Aurekana/SwBus/3D-STL/ChargeNub.dxf

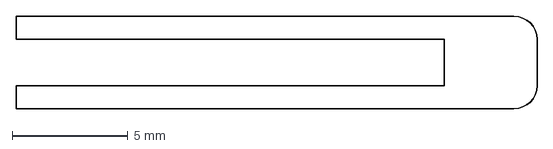
[picture p17: CAD file, 2020-02-20]
3D-STL/ChargeNub.dxf
22.5 x 4.00 mm
