Aurekana/SwBus/3D-STL/23-Cylinder.stl

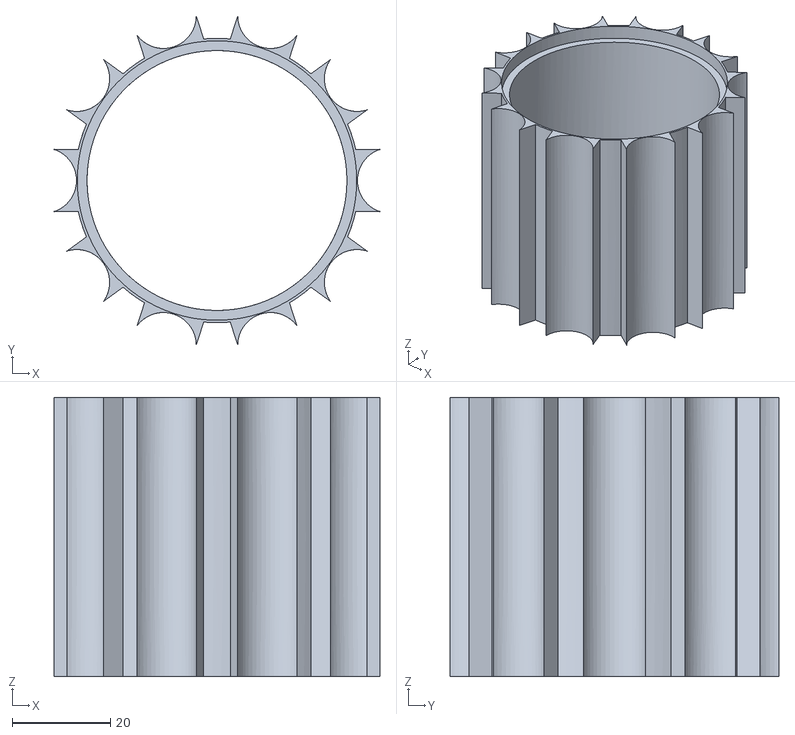
[picture p18: CAD file, 2020-02-20]
3D-STL/23-Cylinder.stl
66.4 x 67.1 x 57.0
