Aurekana/SwBus/3D-STL/19a-StockBack.stl

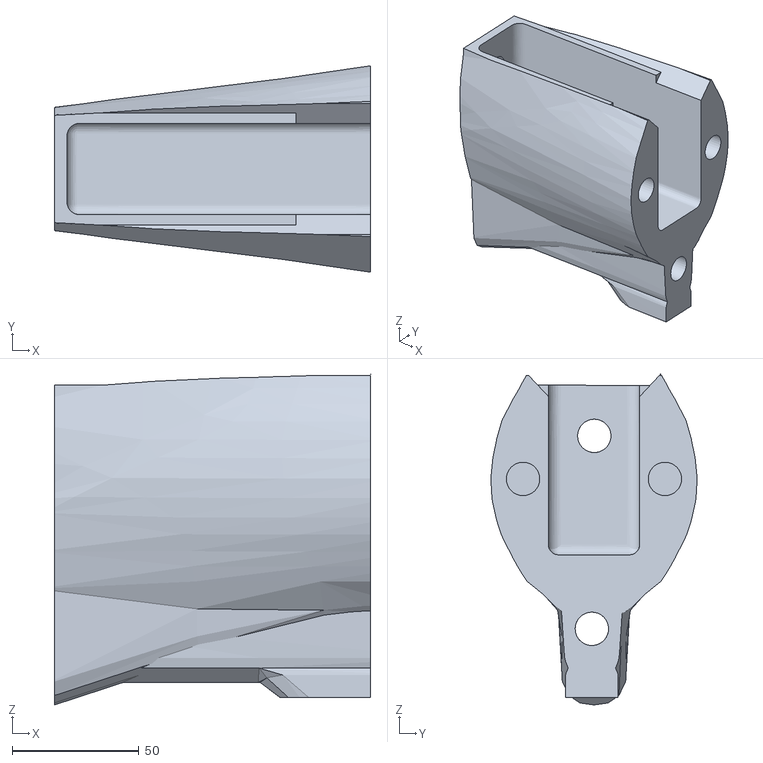
[picture p19: CAD file, 2020-02-20]
3D-STL/19a-StockBack.stl
125.0 x 81.6 x 130.8
