Aurekana/SwBus/3D-STL/33-hud.stl

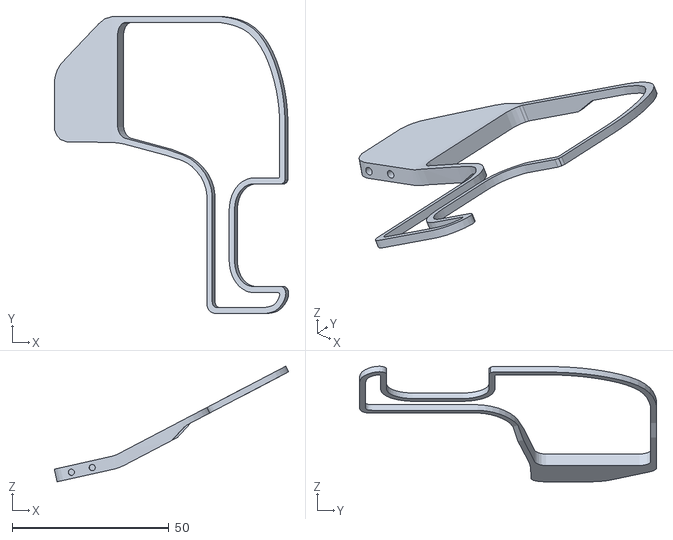
[picture p20: CAD file, 2020-02-20]
3D-STL/33-hud.stl
74.7 x 94.7 x 36.9
