Aurekana/SwBus/3D-STL/19-StockBack.stl

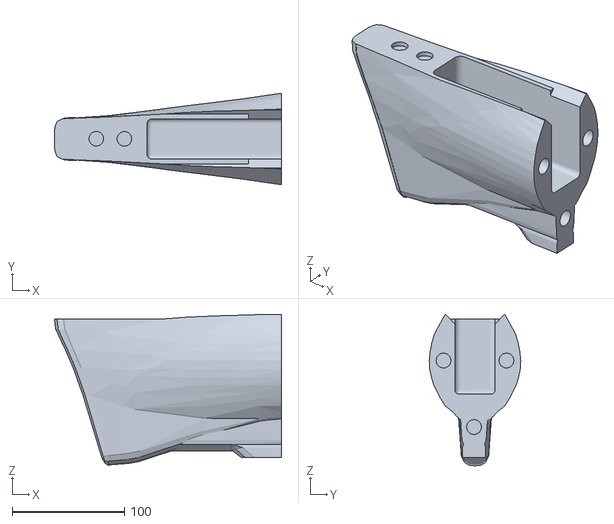
[picture p21: CAD file, 2020-02-20]
3D-STL/19-StockBack.stl
202.3 x 81.6 x 135.4
