Aurekana/SwBus/3D-STL/31-BatCover.stl

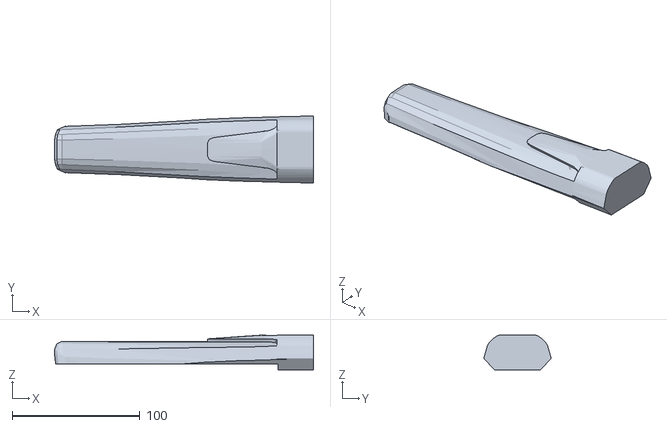
[picture p22: CAD file, 2020-02-20]
3D-STL/31-BatCover.stl
203.1 x 52.7 x 27.3
