Aurekana/SwBus/3D-STL/27b-MagCover.stl

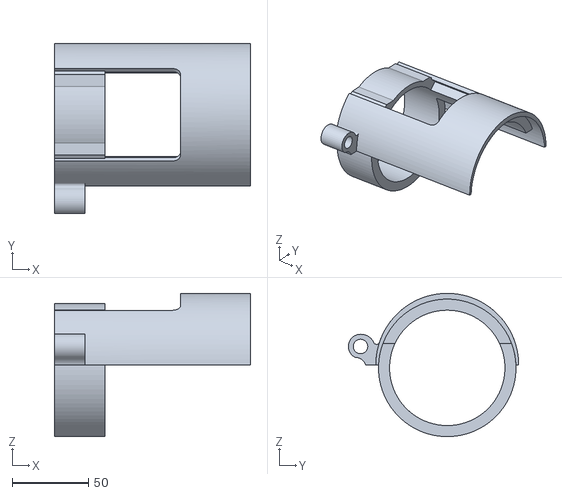
[picture p23: CAD file, 2020-02-20]
3D-STL/27b-MagCover.stl
128.2 x 111.5 x 93.8
