Aurekana/SwBus/3D-STL/30ORCUT-ChargePlate.stl

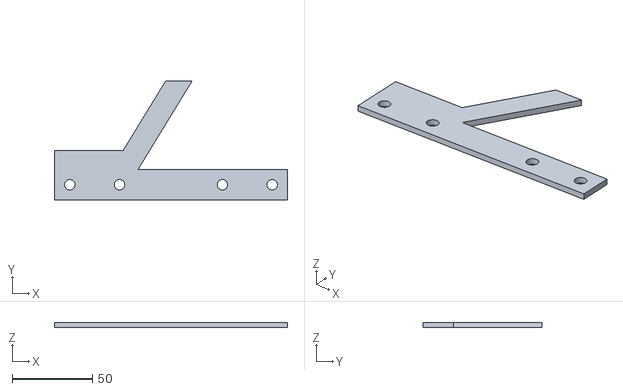
[picture p24: CAD file, 2020-02-20]
3D-STL/30ORCUT-ChargePlate.stl
145.0 x 74.1 x 3.17
