Aurekana/SwBus/3D-STL/28-C-Mag_Cap_60.stl

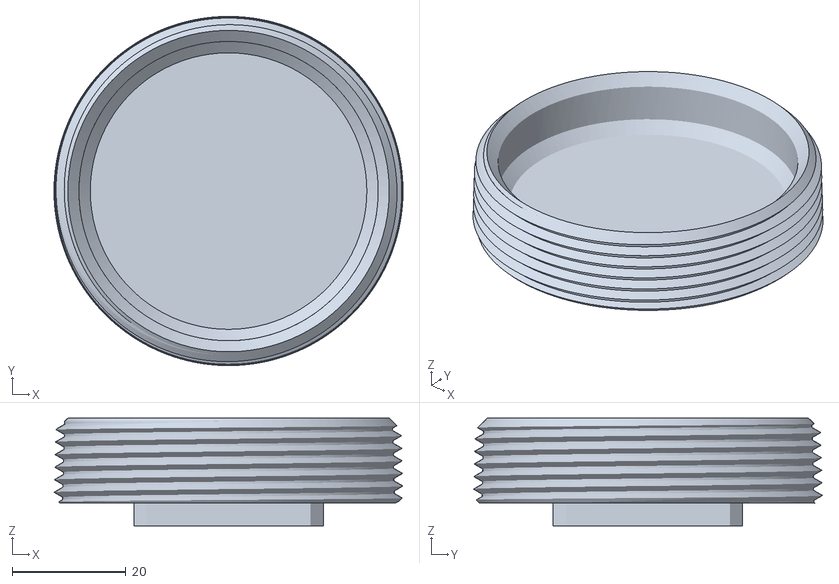
[picture p25: CAD file, 2020-02-20]
3D-STL/28-C-Mag_Cap_60.stl
61.3 x 61.4 x 18.9
