Aurekana/SwBus/3D-STL/hud.dxf

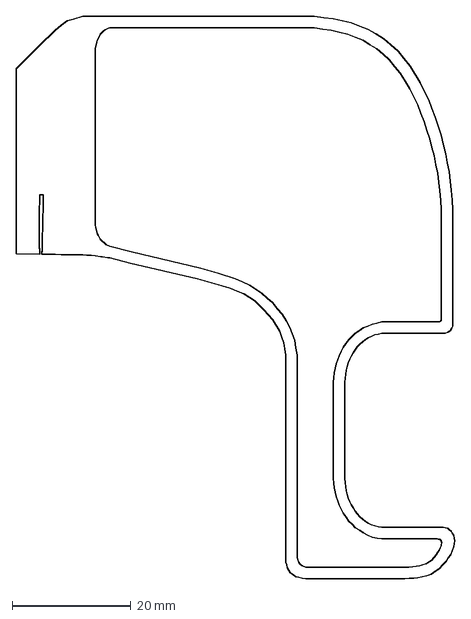
[picture p26: CAD file, 2020-02-20]
3D-STL/hud.dxf
73.8 x 94.7 mm
