Aurekana/SwBus/3D-STL/19b-BackStock.stl

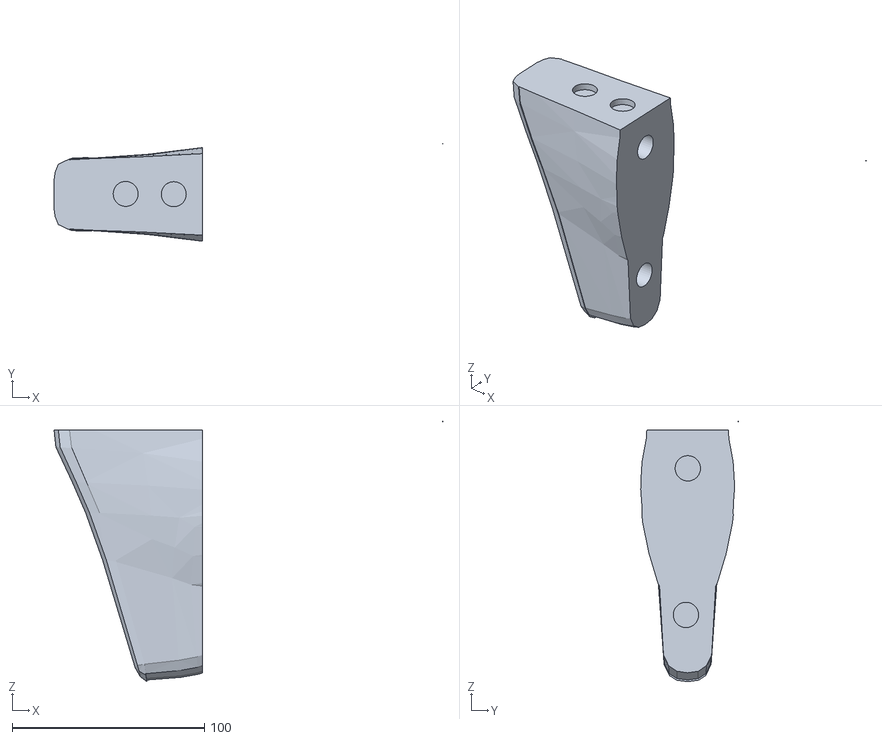
[picture p27: CAD file, 2020-02-20]
3D-STL/19b-BackStock.stl
202.3 x 50.7 x 135.4
