Aurekana/SwBus/3D-STL/Handle_cut.dxf

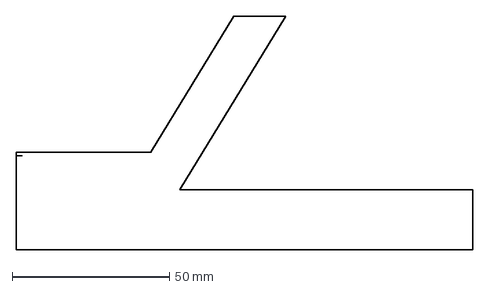
[picture p28: CAD file, 2020-02-20]
3D-STL/Handle_cut.dxf
145.0 x 74.1 mm
