Aurekana/SwBus/3D-STL/28z-Magazine_Beer.stl

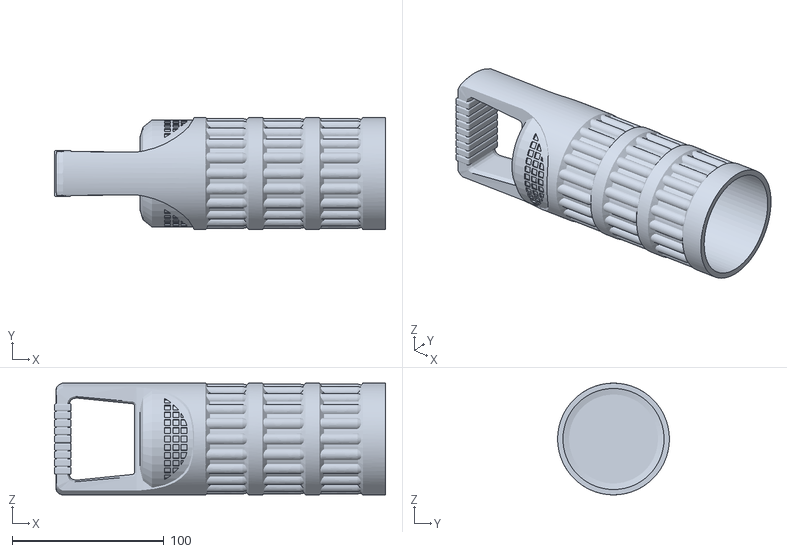
[picture p29: CAD file, 2020-02-20]
3D-STL/28z-Magazine_Beer.stl
217.8 x 73.5 x 73.5
