Aurekana/SwBus/3D-STL/17-MagBack.stl

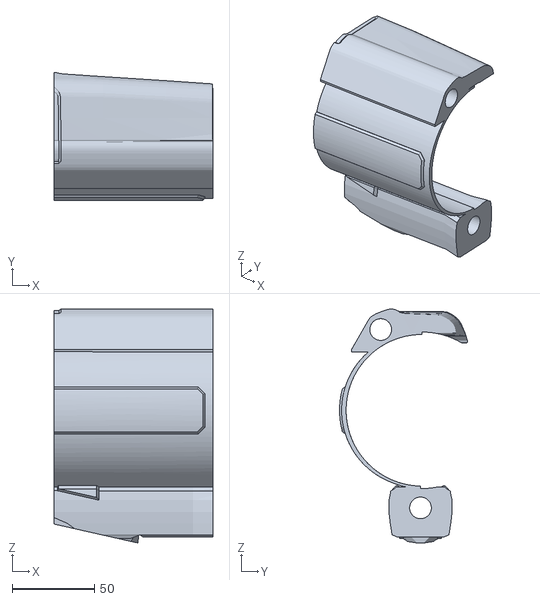
[picture p30: CAD file, 2020-02-20]
3D-STL/17-MagBack.stl
96.4 x 77.6 x 142.0
