Aurekana/SwBus/3D-STL/28zz-Mag-Cont.stl

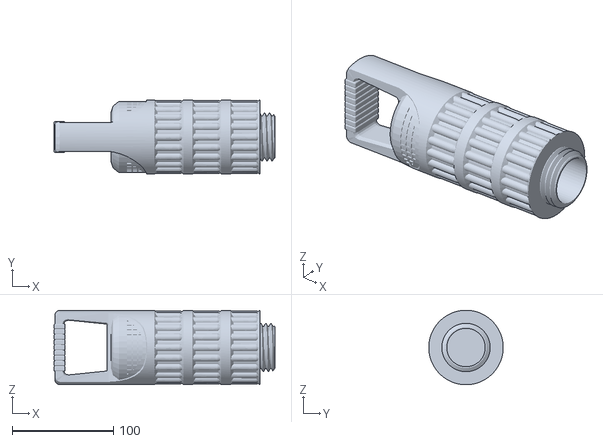
[picture p31: CAD file, 2020-02-20]
3D-STL/28zz-Mag-Cont.stl
218.3 x 73.5 x 73.5
