Aurekana/SwBus/3D-STL/25-Grip.stl

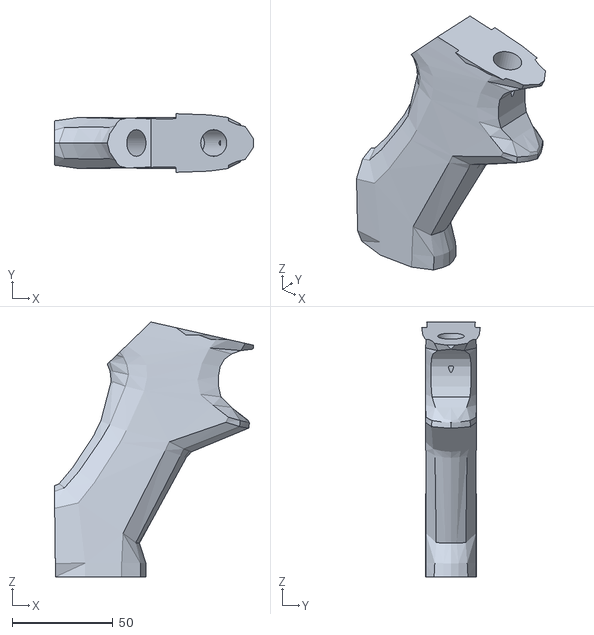
[picture p32: CAD file, 2020-02-20]
3D-STL/25-Grip.stl
98.8 x 29.1 x 126.4
