Aurekana/SwBus/3D-STL/28-Magazine_150.stl

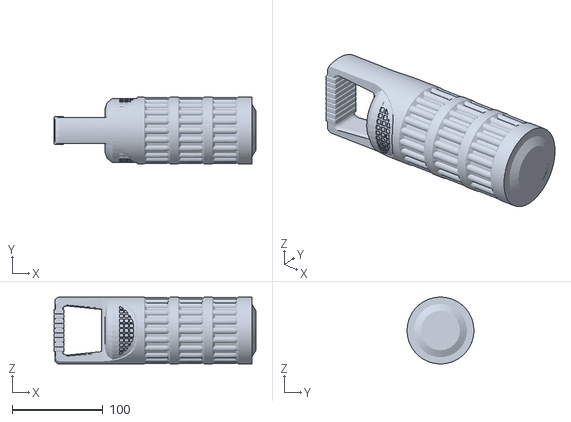
[picture p33: CAD file, 2020-02-20]
3D-STL/28-Magazine_150.stl
222.3 x 73.5 x 73.5
