Aurekana/SwBus/3D-STL/27-MagCover.stl

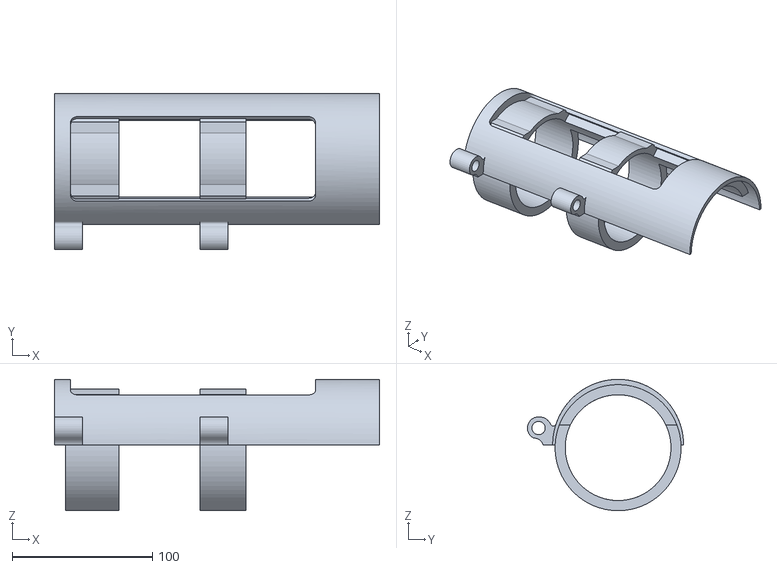
[picture p34: CAD file, 2020-02-20]
3D-STL/27-MagCover.stl
232.0 x 111.5 x 93.7
