Aurekana/SwBus/3D-STL/07-ChargeHandle.stl

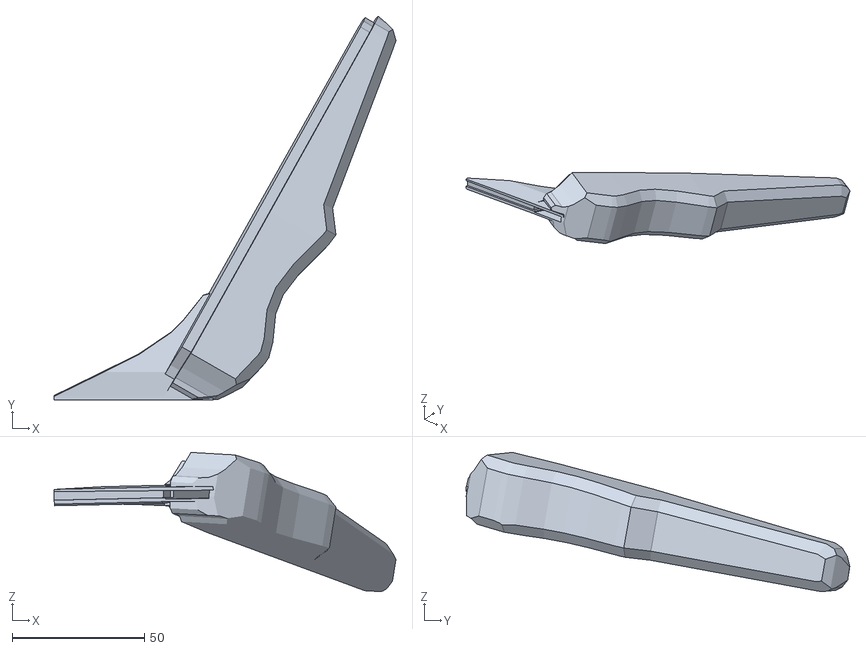
[picture p35: CAD file, 2020-02-20]
3D-STL/07-ChargeHandle.stl
129.2 x 145.0 x 52.6
