Aurekana/SwBus/3D-STL/11-Cylinder.stl

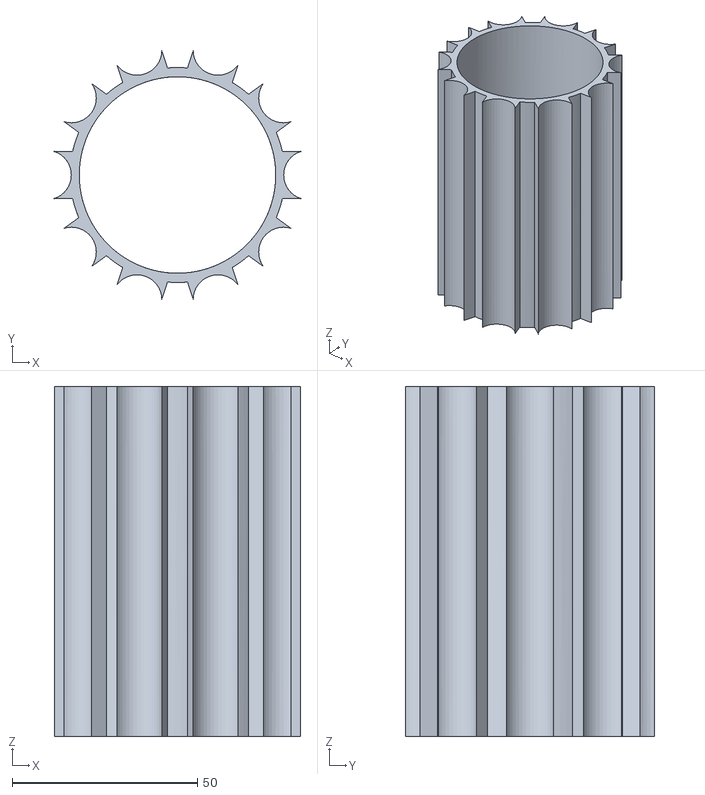
[picture p36: CAD file, 2020-02-20]
3D-STL/11-Cylinder.stl
66.4 x 67.1 x 94.4
