Aurekana/SwBus/3D-STL/15-PotDoor.stl

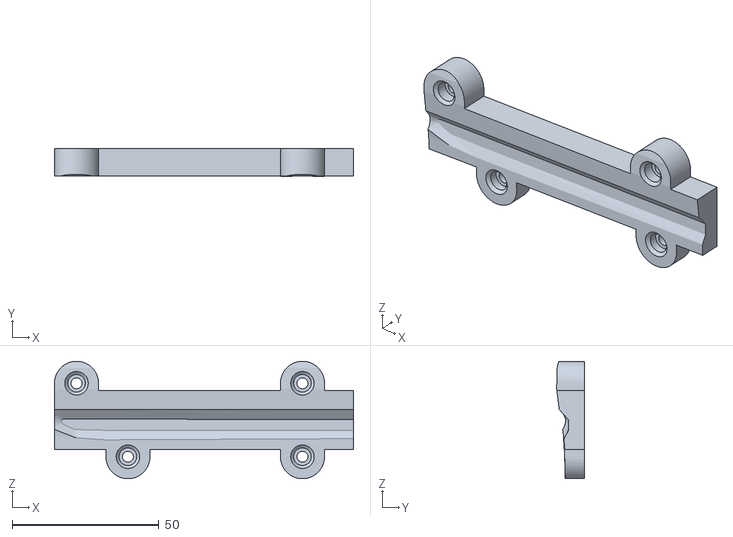
[picture p37: CAD file, 2020-02-20]
3D-STL/15-PotDoor.stl
101.8 x 9.44 x 40.0
