Aurekana/SwBus/3D-STL/09-ChargeUpper.stl

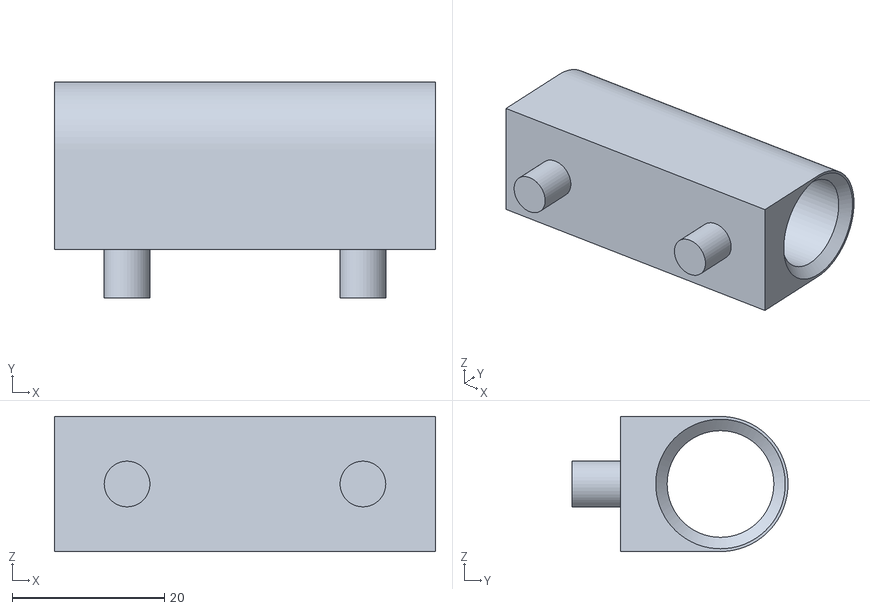
[picture p38: CAD file, 2020-02-20]
3D-STL/09-ChargeUpper.stl
50.0 x 28.4 x 17.7
