Aurekana/SwBus/3D-STL/10-Ring3.stl

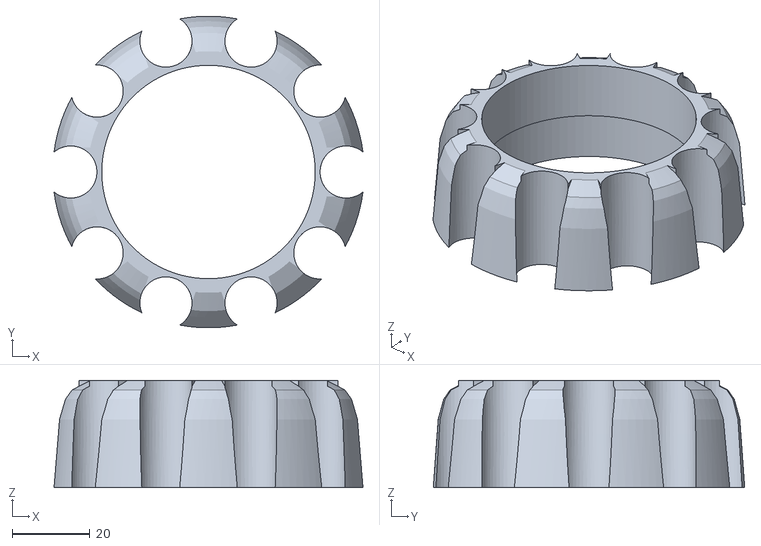
[picture p39: CAD file, 2020-02-20]
3D-STL/10-Ring3.stl
79.3 x 80.0 x 27.5
