Aurekana/SwBus/3D-STL/13-Spacer.stl

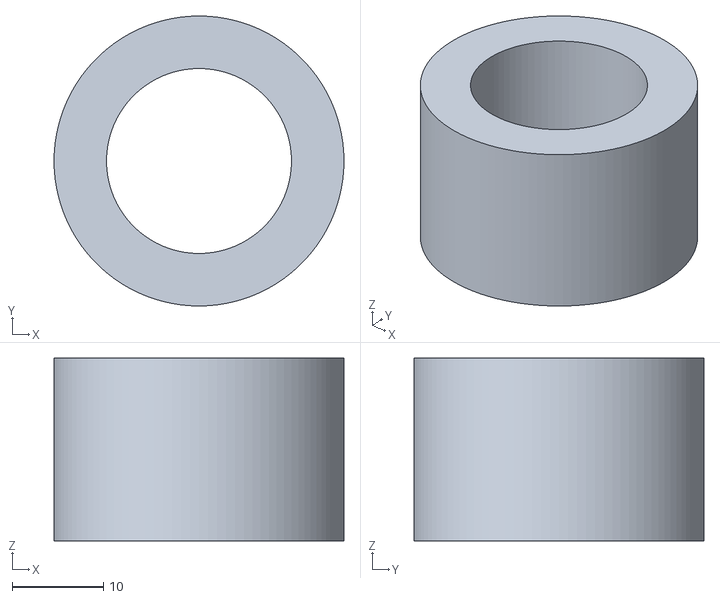
[picture p40: CAD file, 2020-02-20]
3D-STL/13-Spacer.stl
31.8 x 31.8 x 20.0
