Aurekana/SwBus/3D-STL/08-ChargeLower.stl

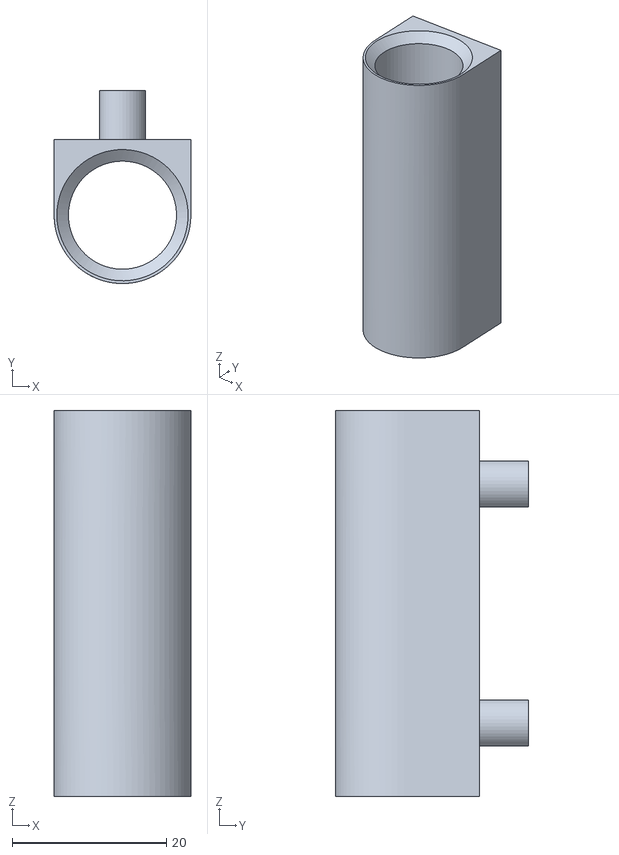
[picture p41: CAD file, 2020-02-20]
3D-STL/08-ChargeLower.stl
17.7 x 25.0 x 50.0
