Aurekana/SwBus/3D-STL/14-Ring2.stl

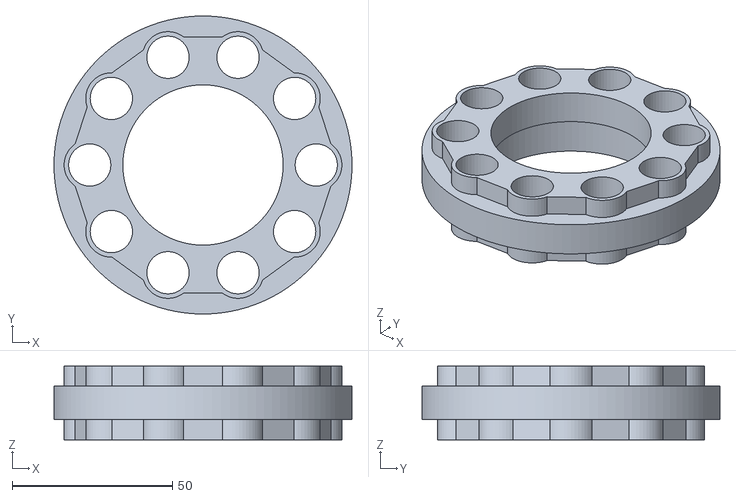
[picture p42: CAD file, 2020-02-20]
3D-STL/14-Ring2.stl
93.0 x 93.0 x 23.0
