Aurekana/SwBus/3D-STL/04-PotDoor.stl

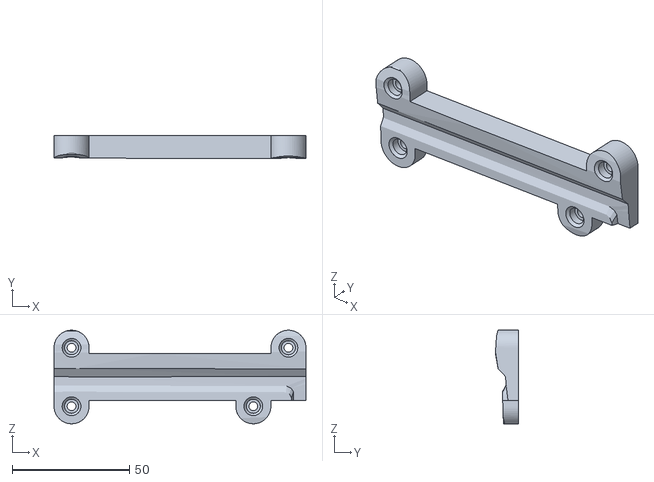
[picture p43: CAD file, 2020-02-20]
3D-STL/04-PotDoor.stl
107.7 x 9.87 x 40.0
