Aurekana/SwBus/3D-STL/01-Front.stl

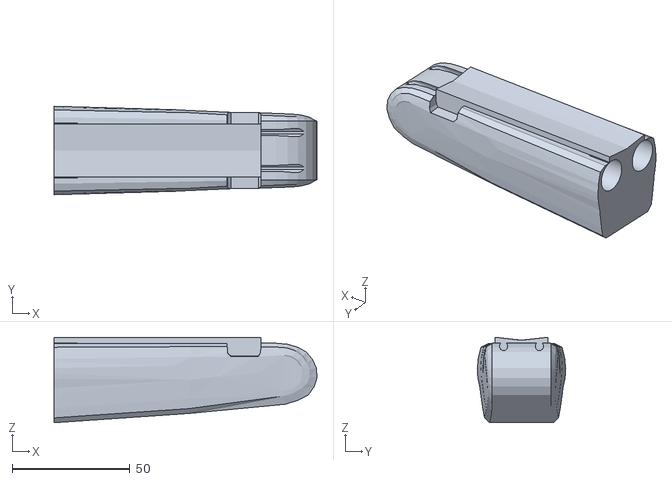
[picture p44: CAD file, 2020-02-20]
3D-STL/01-Front.stl
111.6 x 37.6 x 36.3
