Aurekana/SwBus/3D-STL/05-Front.stl

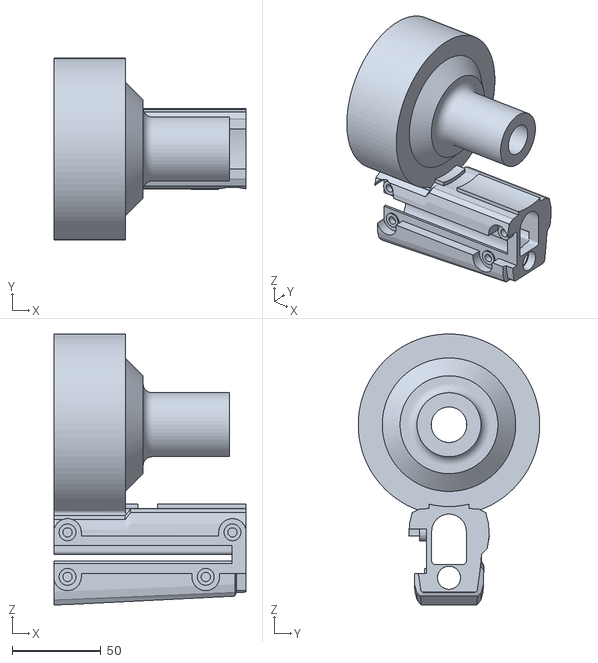
[picture p45: CAD file, 2020-02-20]
3D-STL/05-Front.stl
107.7 x 102.0 x 152.3
