Aurekana/SwBus/3D-STL/02-Front.stl

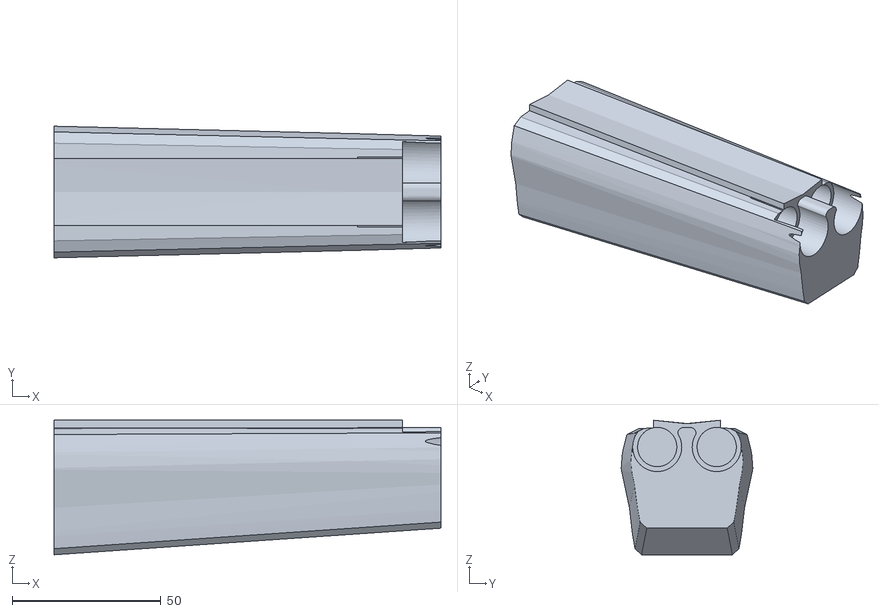
[picture p46: CAD file, 2020-02-20]
3D-STL/02-Front.stl
130.0 x 44.2 x 45.2
