Aurekana/SwBus/3D-STL/03-Front.stl

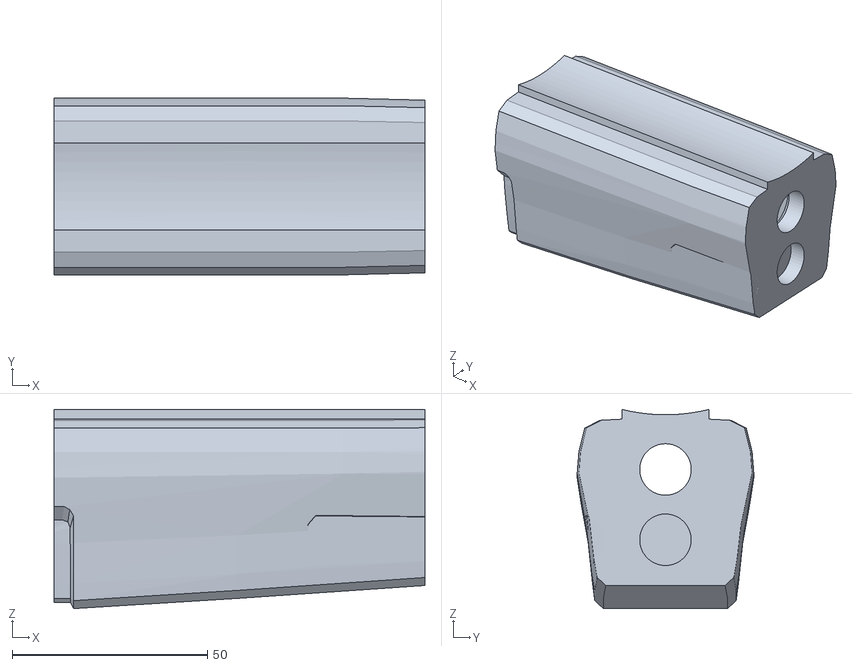
[picture p47: CAD file, 2020-02-20]
3D-STL/03-Front.stl
95.0 x 45.3 x 51.0
