Aurekana/SwBus/3D-STL/06-Ring4.stl

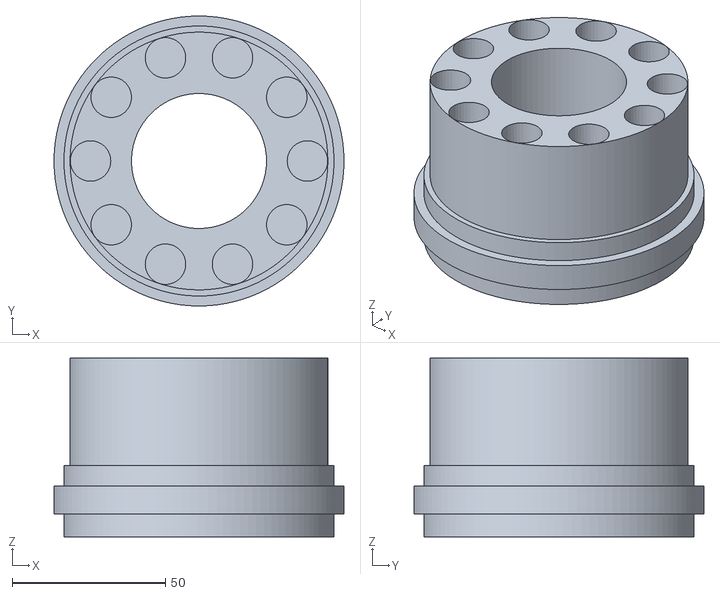
[picture p48: CAD file, 2020-02-20]
3D-STL/06-Ring4.stl
94.5 x 94.5 x 58.2
