Aurekana/SwBus/Assembly/001-Charge_Handle_Assembly.PNG

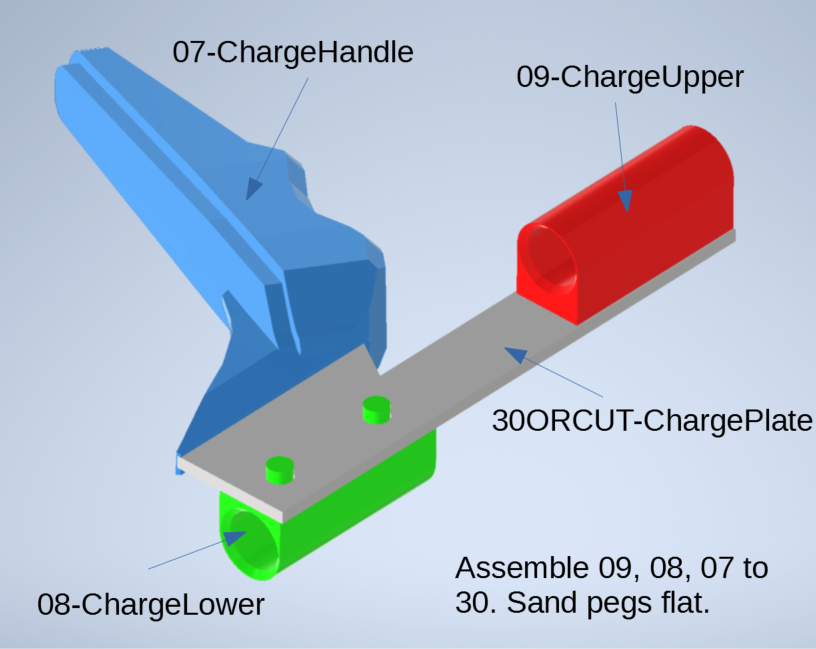
Assembly/001-Charge_Handle_Assembly.PNG
