Aurekana/SwBus/Assembly/002B-Trigger_Wiring_Guide.PNG

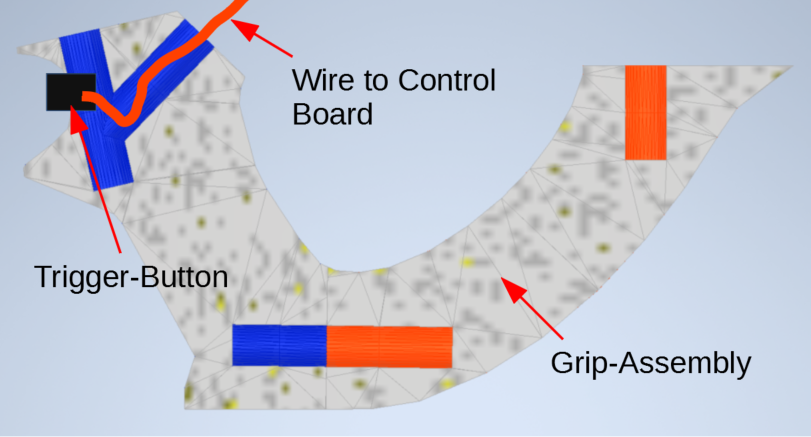
Assembly/002B-Trigger_Wiring_Guide.PNG
