Aurekana/SwBus/Assembly/003-Heat_Set_Insert_Install.PNG

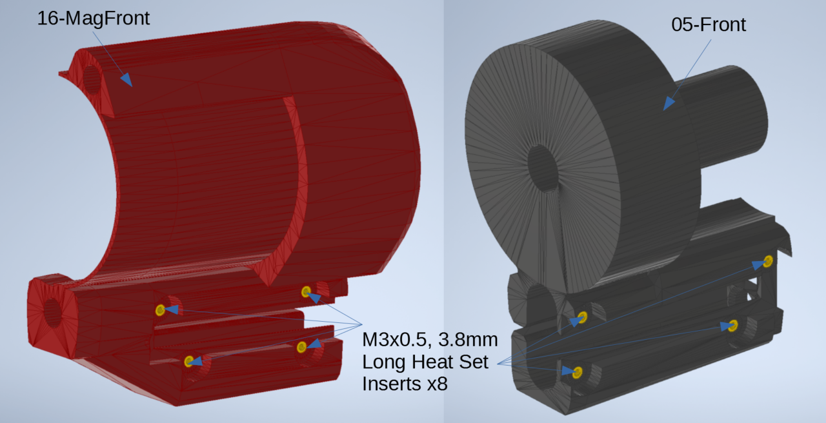
Assembly/003-Heat_Set_Insert_Install.PNG
