Aurekana/SwBus/Assembly/004-Charge_Handle_to_Body_Assembly.PNG

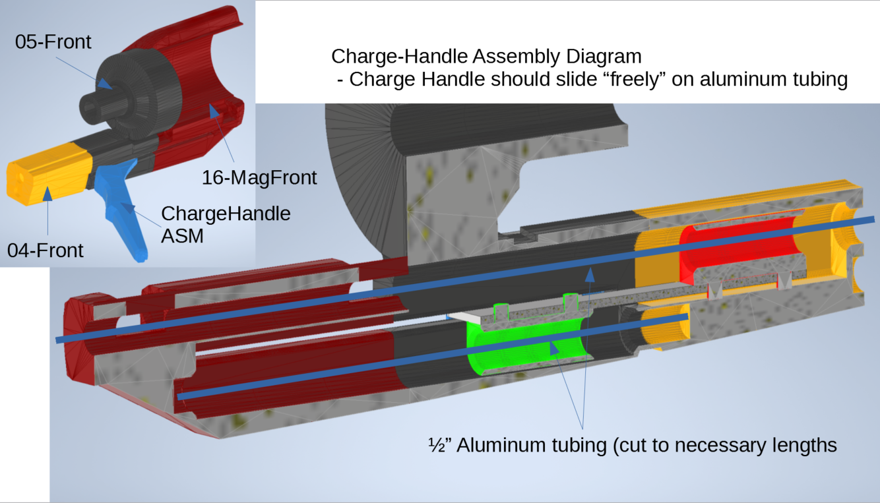
Assembly/004-Charge_Handle_to_Body_Assembly.PNG
