Aurekana/SwBus/Assembly/005A-Mag_Cover_Assembly.PNG

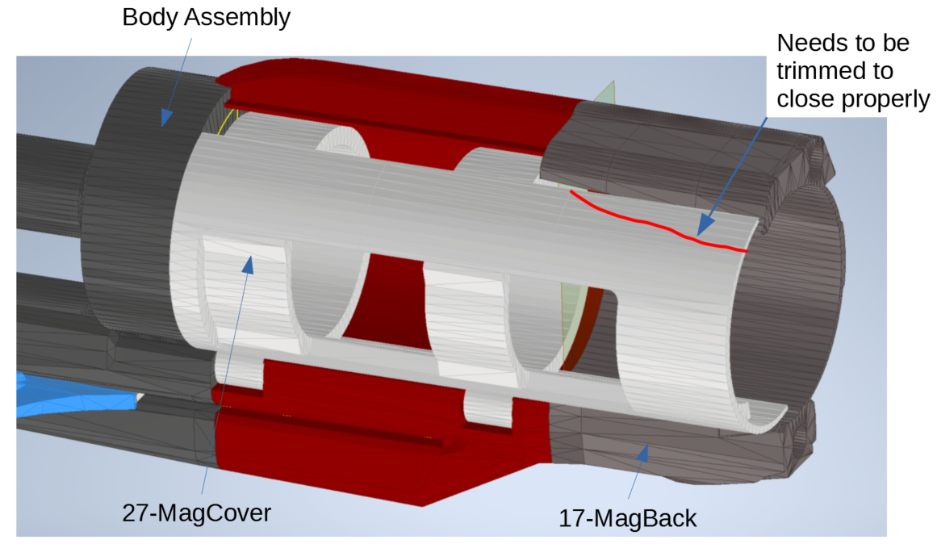
Assembly/005A-Mag_Cover_Assembly.PNG
