Aurekana/SwBus/Assembly/005B-Mag_Cover_Rod_Install.PNG

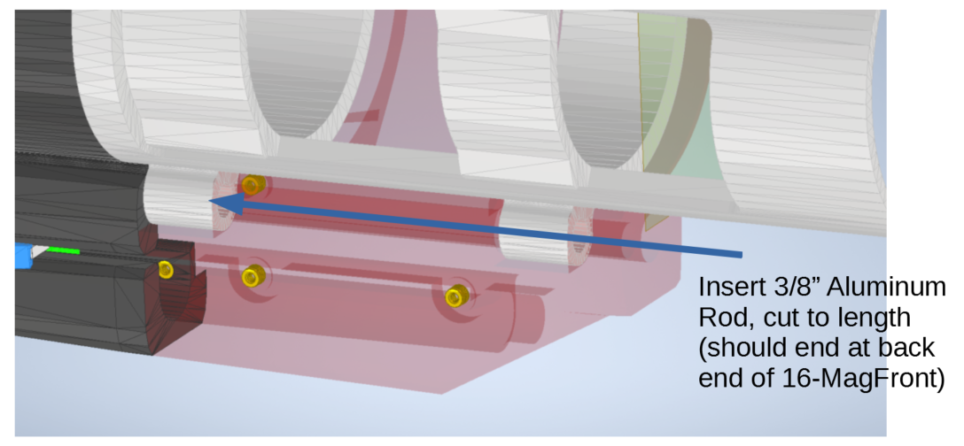
Assembly/005B-Mag_Cover_Rod_Install.PNG
