Aurekana/SwBus/Assembly/006A-StockFront_Install.PNG

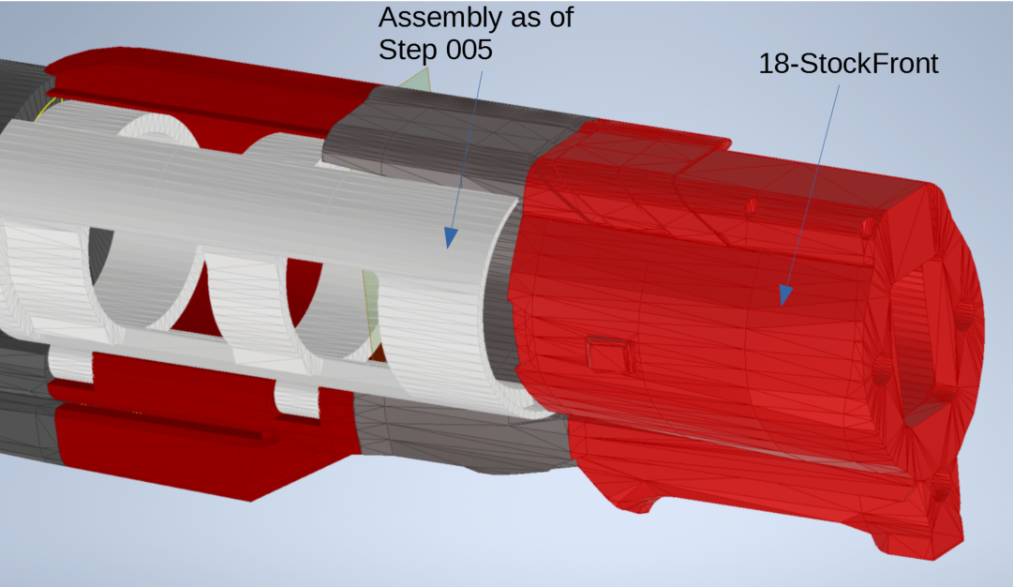
Assembly/006A-StockFront_Install.PNG
