Aurekana/SwBus/Assembly/006C-Wire_Routing_II.PNG

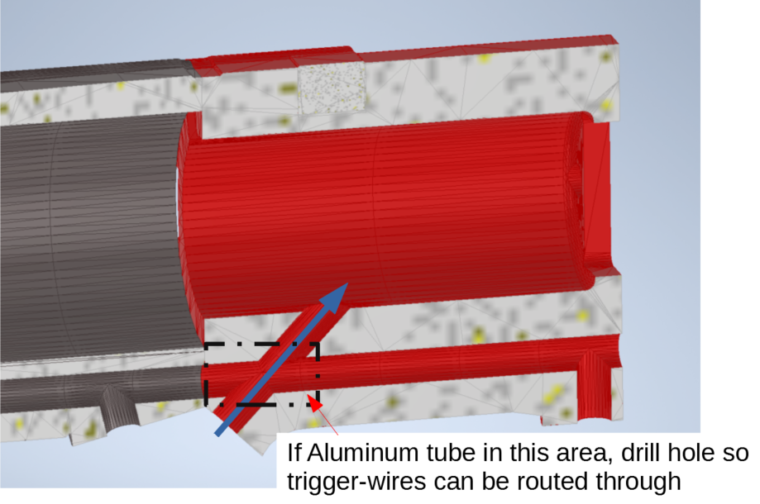
Assembly/006C-Wire_Routing_II.PNG
