Aurekana/SwBus/Assembly/007-Grip_Assembly_Install.PNG

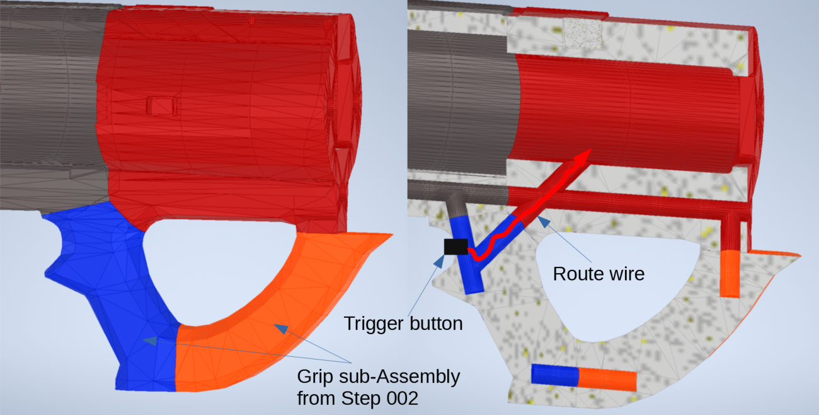
Assembly/007-Grip_Assembly_Install.PNG
