Aurekana/SwBus/Assembly/008-Stock_Install.PNG

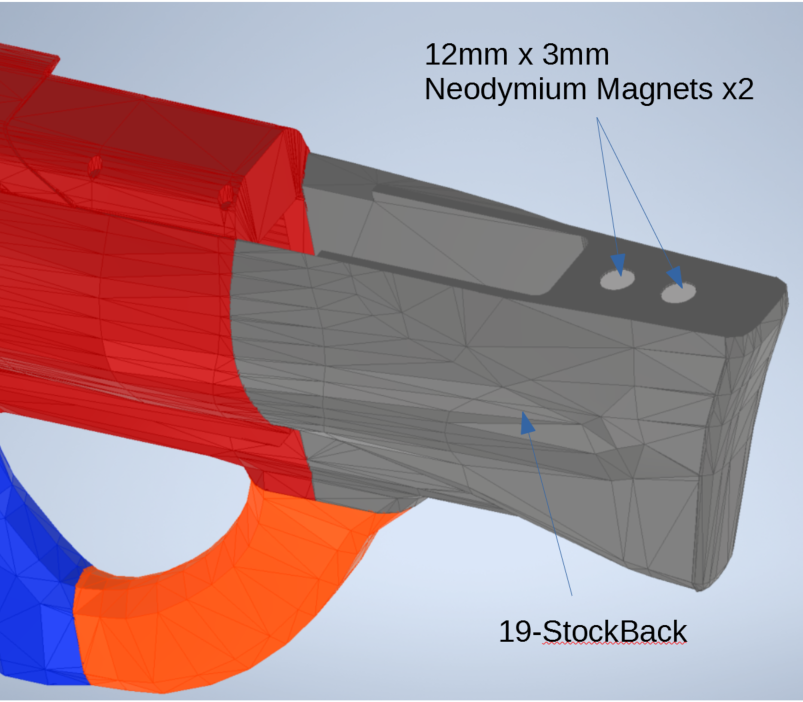
Assembly/008-Stock_Install.PNG
