Aurekana/SwBus/Assembly/009-Front_Final_Install.PNG

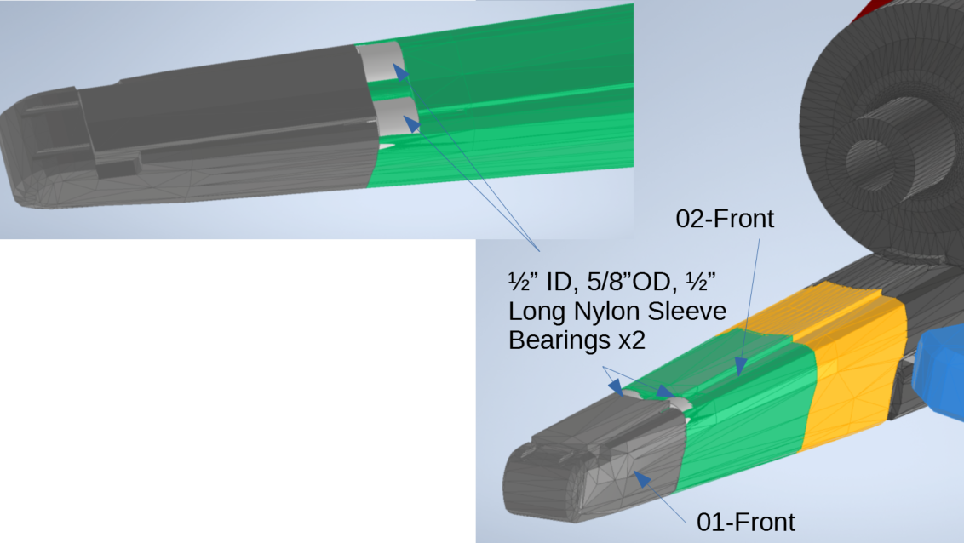
Assembly/009-Front_Final_Install.PNG
