Aurekana/SwBus/Assembly/011-Motor_Mount_Routing.PNG

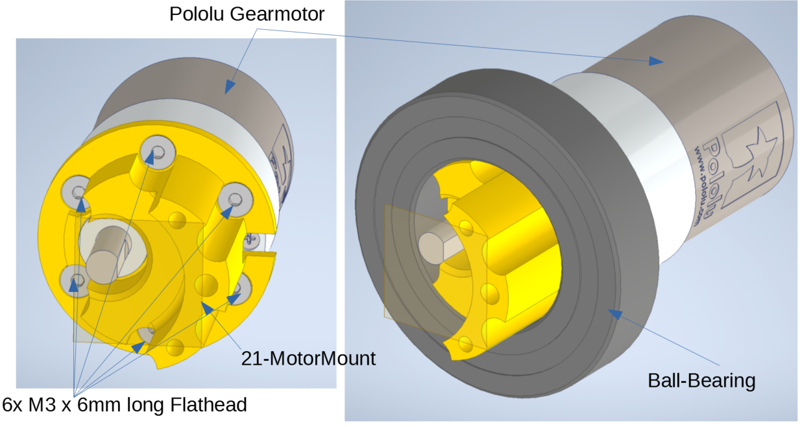
Assembly/011-Motor_Mount_Routing.PNG
