Aurekana/SwBus/Assembly/013-Gear_Install.PNG

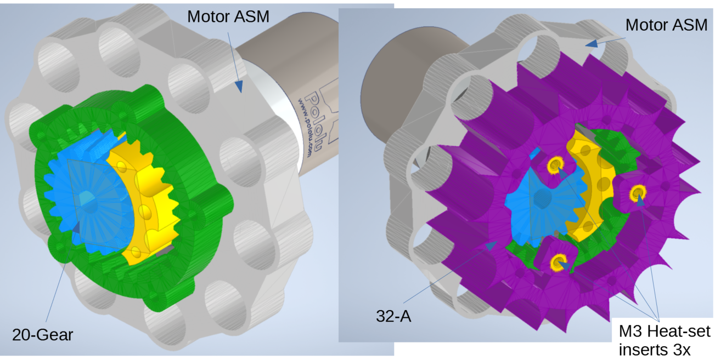
Assembly/013-Gear_Install.PNG
