Aurekana/SwBus/Assembly/014-Slip_Ring_Wire_Routing.PNG

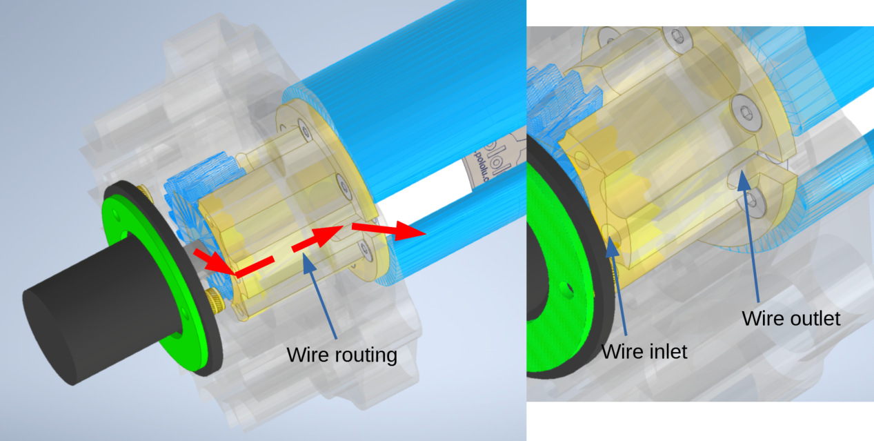
Assembly/014-Slip_Ring_Wire_Routing.PNG
