Aurekana/SwBus/Assembly/015-Motor_Sleeve_Install.PNG

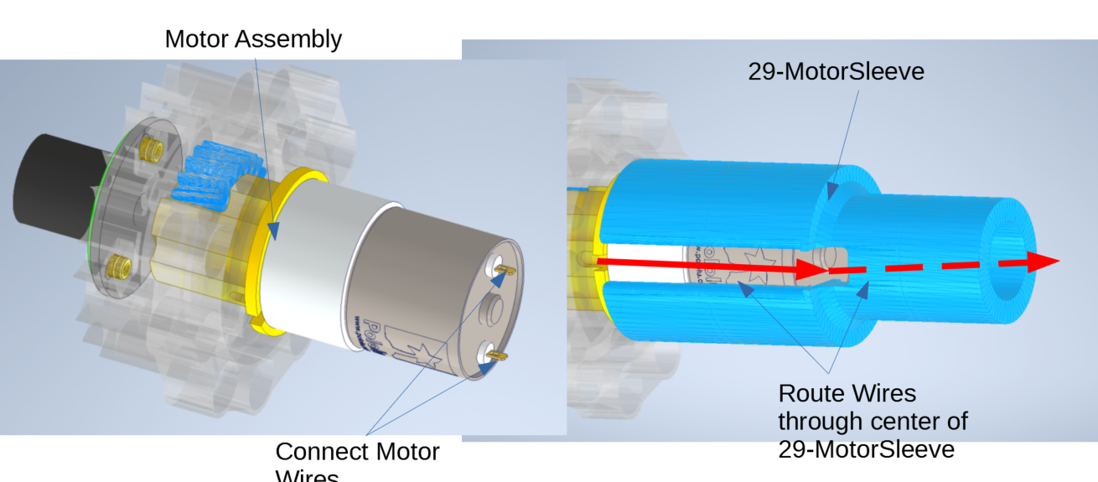
Assembly/015-Motor_Sleeve_Install.PNG
