Aurekana/SwBus/Assembly/016-Cantilever_Tube.PNG

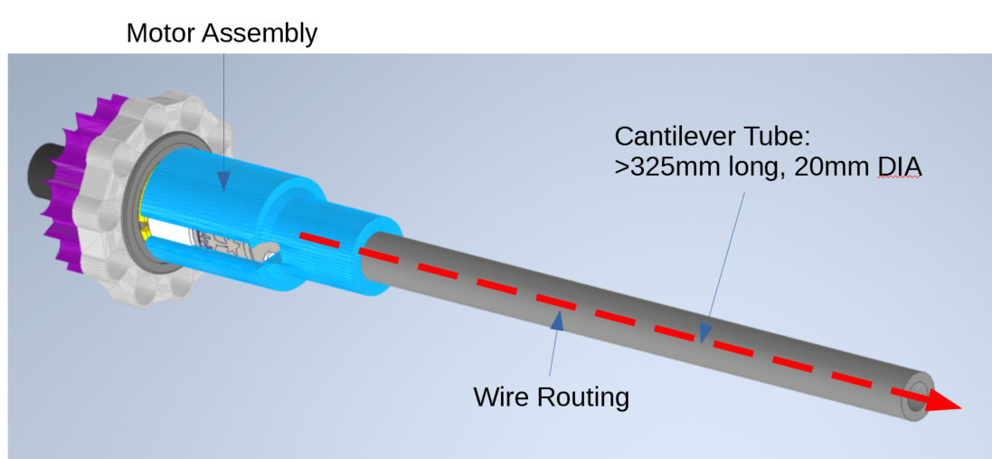
Assembly/016-Cantilever_Tube.PNG
