Aurekana/SwBus/Assembly/017-Cylinder_Install.PNG

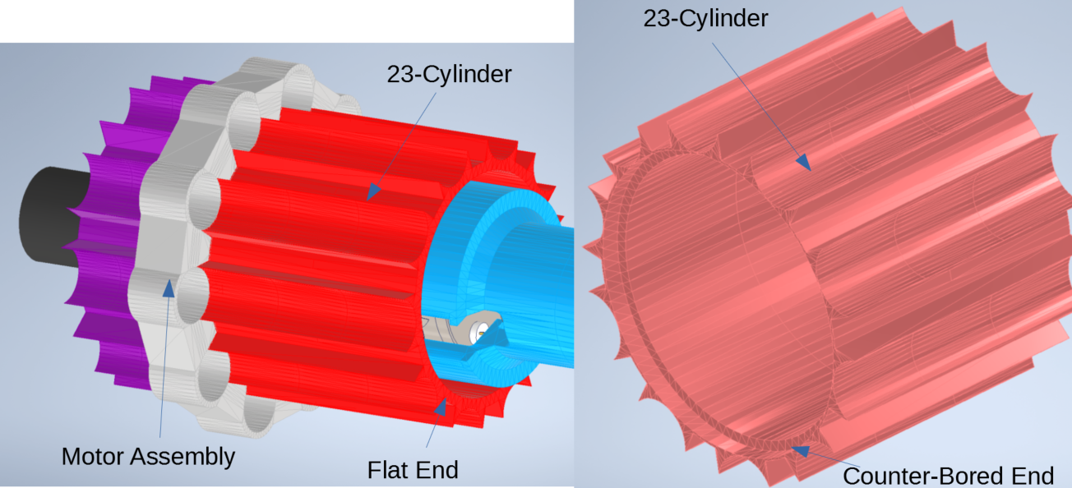
Assembly/017-Cylinder_Install.PNG
