Aurekana/SwBus/Assembly/019-Long_Cylinder_Install.PNG

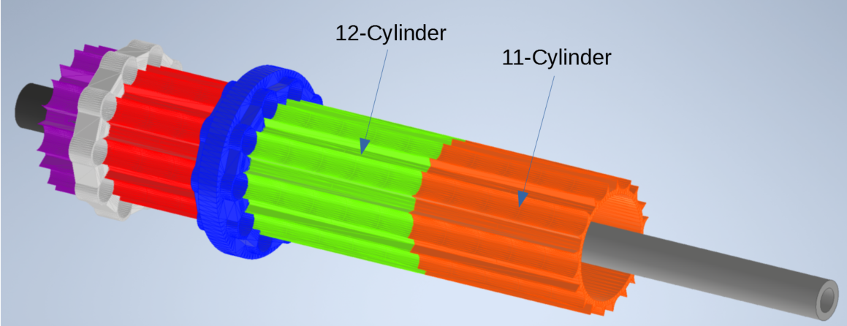
Assembly/019-Long_Cylinder_Install.PNG
