Aurekana/SwBus/Assembly/020-Ball_Bearing_Install.PNG

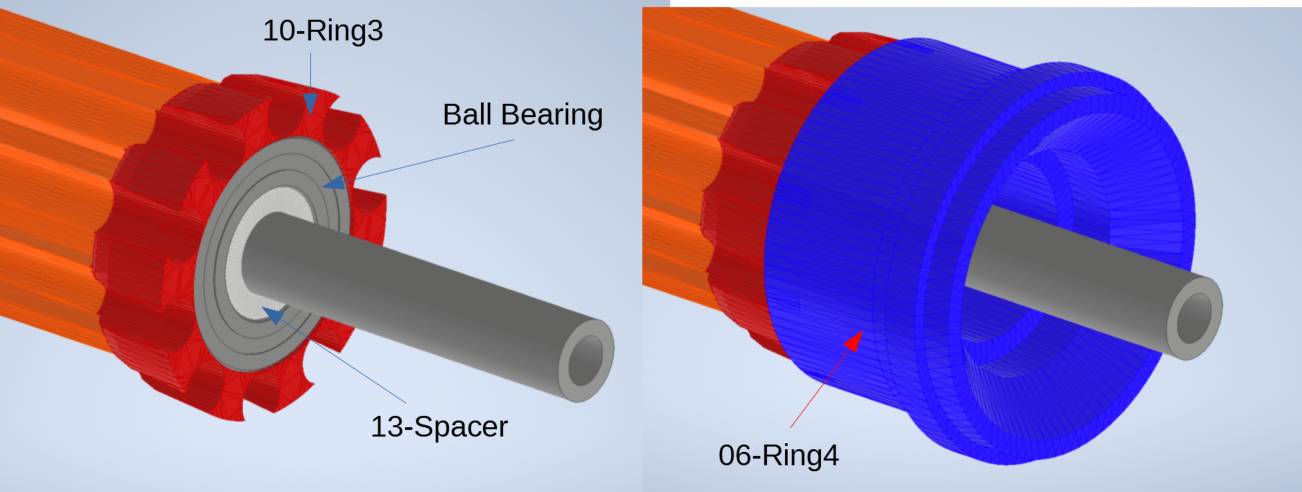
Assembly/020-Ball_Bearing_Install.PNG
