Aurekana/SwBus/Assembly/021-Barrel_Assembly.PNG

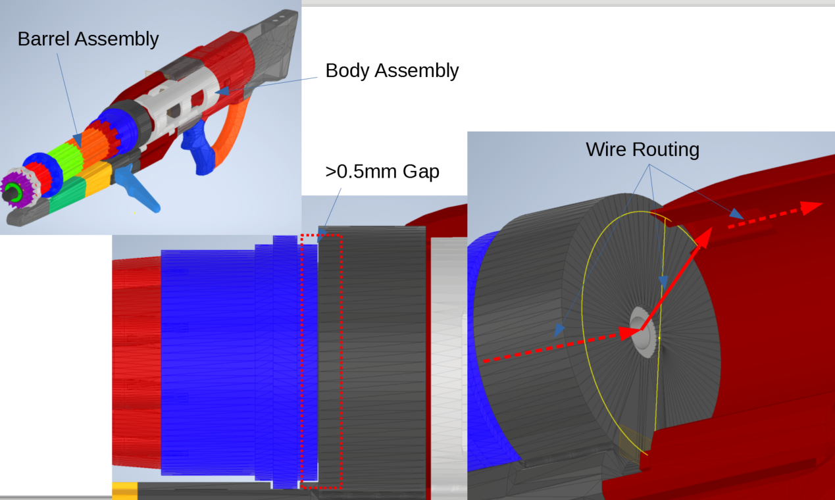
Assembly/021-Barrel_Assembly.PNG
