Aurekana/SwBus/Assembly/022A-Electronics_Assembly.PNG

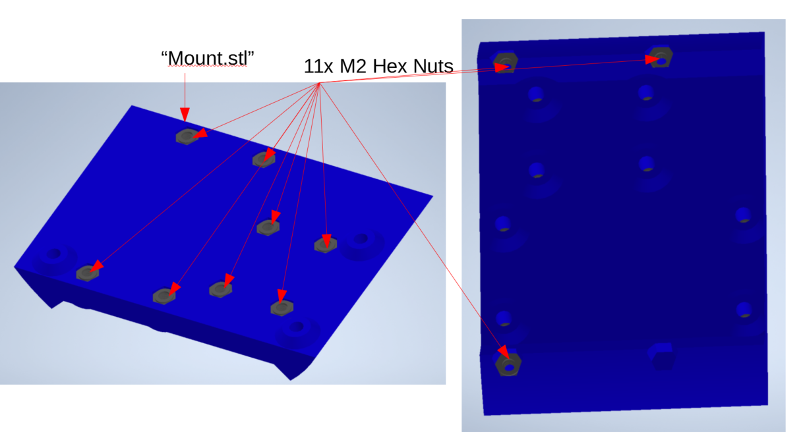
Assembly/022A-Electronics_Assembly.PNG
