Aurekana/SwBus/Assembly/022B-Electronics Assembly.PNG

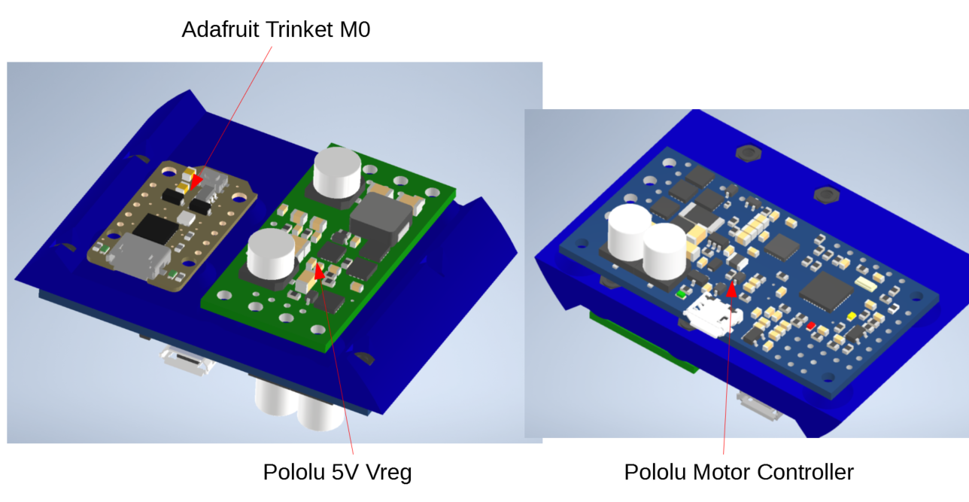
Assembly/022B-Electronics Assembly.PNG
