Aurekana/SwBus/Assembly/023-Battery_Harness.PNG

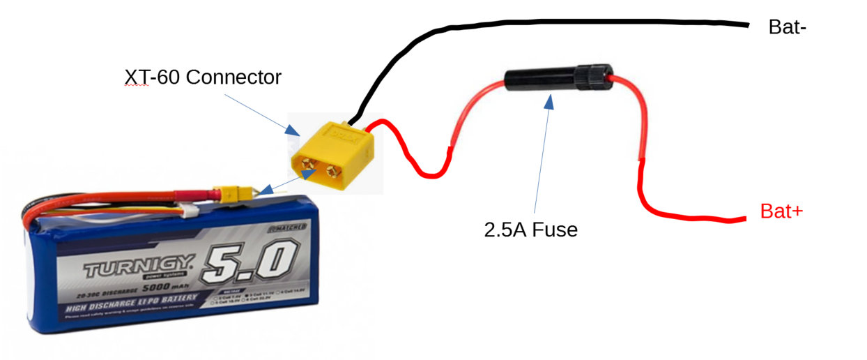
Assembly/023-Battery_Harness.PNG
