Aurekana/SwBus/Assembly/023B-System_Layout.PNG

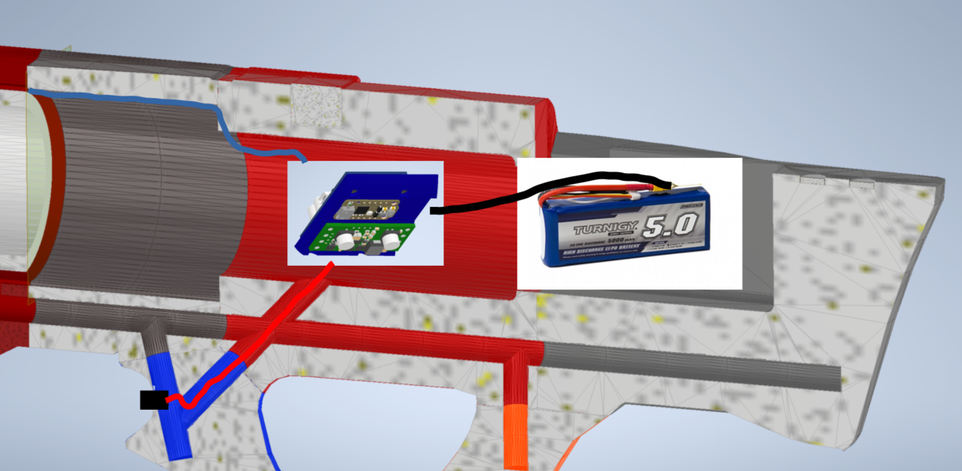
Assembly/023B-System_Layout.PNG
