Aurekana/SwBus/Assembly/024-PotDoors.PNG

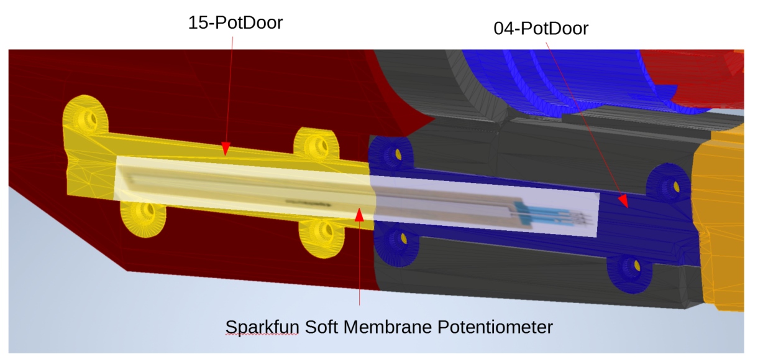
Assembly/024-PotDoors.PNG
