Aurekana/SwBus/Assembly/Asm_wout_barrels.PNG

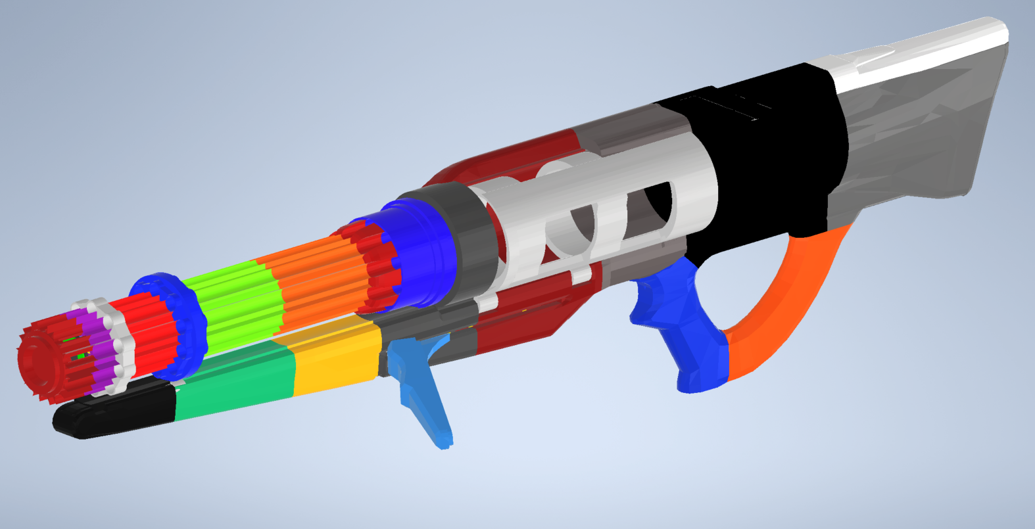
Assembly/Asm_wout_barrels.PNG
